JosVanEijndhoven/diyaudio-dac-preamp/dacxo-hw/PCBs/PCB-dacxo/kicad/daconv.sch

## KiCad design dacxo-hw/PCBs/PCB-dacxo/kicad/daconv.sch (2025-12-10)

Schematic: daconv.sch

Parts:
C301, C305, C336, C337: 100nF; C0805
C302, C304, C307, C314, C322, C323, C332, C334, C338: 1uF; C0805
C303, C306, C308, C311, C312, C313, C315, C318, C319, C325, C328, C331, C333: 10nF; C0805
C309, C310, C316, C317: 47uF; SM1206POL
C320, C321, C339: 1mF; CL-10
C324, C327: 1nF; C0805
C326, C329, C330, C335: 10uF; SM1206POL
D301, D302, D303: B130; DO214
FB301, FB302, FB303, FB304: FILTER; L0805
K301: PCM-audio_L; SIL-3-screw
K302: PCM-audio_R; SIL-3-screw
P301: CONN_4; SIL-4
P302: CONN_8; SIL-8
Q301, Q302: BCP54; SOT223-BCP
R303, R309: 10k; MMB0207
R306: 47R; R0805
R307: 3k3; R0805
R308, R316: 100R; R0805
R310, R314, R315: 1.5k; R0805
R312: 470R; R0805
R317, R318, R319: 470; R0805
R320: 100; R0805
U301, U305: PCM1792A; SSOP28
U302: ADR381; SOT23
U303: OPA2227; SO8E
U304: STM1816; SOT23
U306: MACHXO2-100; TQFP_100
U307: 74AC174; SO16E

Notes on the sheet:
I2S format: MSB first, wck low means left audio, 2x32 bitclk's in a wck period. wck and data change at falling edge of bitclk, are sampled at rising edge. MSB bit transfered at 2nd rising edge of bitclk after wck transient.
NP0
16V
2x7Vac
Analog supply
low noise
tantaal SMD elco AVX F930J476MAA
16V SMD 10mm dia
addr0: differentiate or unite both PCMs
