JosVanEijndhoven/diyaudio-dac-preamp/dacxo-hw/PCBs/PCB-dacxo/kicad/dacwolfs.sch

## KiCad design dacxo-hw/PCBs/PCB-dacxo/kicad/dacwolfs.sch (2025-12-10)

Schematic: dacwolfs.sch

Parts:
C201, C203, C205, C211, C213, C219: 100nF; C0805
C202, C204, C206, C207, C208, C212, C214, C215, C216: 10uF; SM1206POL
C209, C210, C217, C218: 10nF; C0805
FB201, FB202, FB203: FILTER; L0805
K201: WM-audio-L; SIL-3-screw
K202: WM-audio-R; SIL-3-screw
R202, R203, R204, R205, R206, R207, R208, R209: 470; R0805
R210, R211, R212, R213: 47r; R0805
R214, R215: 4.7k; R0805
U201, U202: WM8741; SSOP28

Notes on the sheet:
C1206C106K4RACAUTO
2x470 ohm to 10nF gives 67kHz bandwidth. Audio-grade: C0G dielektricum
WM8741 operated in software mode: status is written by microcontroller. It seems that this device does not support read-back of register data :-(
mount in HW mode
