JosVanEijndhoven/diyaudio-dac-preamp/dacxo-hw/PCBs/PCB-dacxo/kicad/pwr_clk.sch

## KiCad design dacxo-hw/PCBs/PCB-dacxo/kicad/pwr_clk.sch (2025-12-10)

Schematic: pwr_clk.sch

Parts:
C401, C404, C405, C408, C410, C415, C416, C417: 10nF; C0805
C402, C403, C406, C407, C409, C411, C412, C413, C424: 1uF; C0805
C414: 100nF; C0805
C423: 10uF; SM1206POL
C425, C426: 100pF; C0805
D401, D402: B130; DO214
D403, D404, D405, D406, D407: BI_LED; dualled-1210
FB401, FB402, FB403, FB404: FILTER; L0805
P401: 5V-in; SIL-3-screw
P402: I2C-in; SIL-4
P404: CONN_8; SIL-8
P405: test-jtag; SIL-8
P406: test-XO; SIL-8
P407: test-speed; SIL-8
P408: I2S; SIL-4
Q401: NUD3112; SC-74
R401, R402, R403, R404, R405, R418, R419, R420, R421, R422: 4k7; R0805
R406, R407, R408, R409, R410, R412, R414, R415, R416, R417: 330R; R0805
R411, R413: 47R; R0805
U306: MACHXO2-100; TQFP_100
U401: DLP-USB1232H
U403: TS3A5018; SO16E
U404, U407: XO; CCHD-957
U405: 1G99; SSOP8
U406: MC33275-3.3; SOT223-BCP

Notes on the sheet:
USB
in=0 then NC
I2C from controller
5V power in
test pins
45.1584MHz
49.152MHz
CCHD-957
48kHz
96kHz
192kHz: both
clk adjust
LCMXO2-1200HC-4TG100C
reserved for aux I2S input
input switch debounce
pin 8 and 15not on gnd in 201502 PCB!
