JosVanEijndhoven/diyaudio-dac-preamp/dacxo-hw/PCBs/PCB-dacxo/kicad/recvr.sch

## KiCad design dacxo-hw/PCBs/PCB-dacxo/kicad/recvr.sch (2025-12-10)

Schematic: recvr.sch

Parts:
C501, C504, C505, C507, C509: 10nF; C0805
C502, C503, C506, C508, C510: 1uF; C0805
C511, C512, C513, C515, C517: 100nF; C0805
C514: 1nF; C0805
C516: 22nF; C0805
FB501, FB502, FB503: FILTER; L0805
P501: aux-in; SIL-4
P502: DUAL-CINCH; dualphono-kobiconn
R501, R502, R503, R504, R505, R506, R507, R508, R511: 47k; R0805
R509, R510: 47R; R0805
R513, R514, R523, R524: 150; R0805
R520, R529: 1k; R0805
R522: 3k3; R0805
T501, T502: PE-65812NL; SPDIFtrafo-pulse
U306: MACHXO2-100; TQFP_100
U501, U502: TORX; TORX-PLR135
U503: CS8416; SO28

Notes on the sheet:
P4[28] and P4[29] are still avail for UART3 TXD and RXD, are connected to daughterboard pins PAD15 and PAD16. (Maybe some UART should be routed to mainboard IO in next rev.)
PLR135T7
SW mode
HW mode
2xR for SW mode
pull-down resistor on RST was missing
