JosVanEijndhoven/diyaudio-dac-preamp/dacxo-hw/PCBs/PCB-opampout/kicad/audio-left.sch

## KiCad design dacxo-hw/PCBs/PCB-opampout/kicad/audio-left.sch (2025-12-10)

Schematic: audio-left.sch

Parts:
C301, C302: 470pF; Cmica6
K203, K204, K205, K206: CINCH-DUAL; switchcraft-dualcinch
K209, K210, K211, K212, K213, K316: RELAY_G6K_AB; G6K-2F-Y
K301, K302: XLR3-FEMALE; NC3FAH
K307, K308, K309, K310, K311, K312, K313, K314: RELAY_G6K; G6K-2F-Y
K315: XLR3-MALE; NC3MAH
R301, R303, R320, R335: 1k; MMB0207
R302, R334: inf; MMB0207
R304, R314, R321, R331: 470R; MMB0207
R305, R322: 3k9; MMB0207
R306, R323: 0R; MMB0207
R307, R324: 100R; MMB0207
R308, R325: 2k2; MMB0207
R309, R326: 220R; MMB0207
R310, R327: 1k2; MMB0207
R311, R328: 560R; MMB0207
R312, R329: 680R; MMB0207
R313, R318, R330, R336: 1k8; MMB0207
R315, R332: 12K; MMB0207
R316, R333: 390R; MMB0207
R317, R319: 47k; MMB0207
U301: LME49720; DIP-8__300
