JosVanEijndhoven/diyaudio-dac-preamp/dacxo-hw/PCBs/PCB-opampout/kicad/audio-right.sch

## KiCad design dacxo-hw/PCBs/PCB-opampout/kicad/audio-right.sch (2025-12-10)

Schematic: audio-right.sch

Parts:
C201, C203, C205, C207: 10n; Cmica6-w0805
C202, C204, C206, C208: 10n; SM0805
K201: CINCH-DUAL; dualphono-kobiconn
K202: Vin-L; SIL-3
K203, K207: RELAY_G6K; G6K-2F-Y
K204: Vout-L; NC3MAH
K205: Iin-L; SIL-3
K206: Vin-R; SIL-3
K208: Vout-R; NC3MAH
K209: Iin-R; SIL-3
L201, L202, L203, L204: 330uH; SM1210
R201, R206, R210, R211, R212, R216, R221, R222, R223, R228, R232, R233, R234, R238, R243, R244: inf; SMM0204
R202, R203, R204, R208, R209, R213, R214, R218, R219, R220, R224, R225, R226, R230, R231, R235, R236, R240, R241, R242: 2k; SMM0204
R205, R215, R227, R237: 220R; SMM0204
R207, R217, R229, R239: 249; SMM0204
U201, U202, U203, U204: LME49720; DIP-8__300

Notes on the sheet:
TDK NLV32T 331J
G6K-2Y-5
-20dB switch
all 12 of 2k resistors around opamps are 0.1% MELF 0204
Voltage input 2x 2.5Vdc +/- 1.4Vpk
Current input: 2x 12.4mAdc +/- 7.8mApk
all 12 resistors around opamps are 0.1% MELF 0204
