JosVanEijndhoven/diyaudio-dac-preamp/dacxo-hw/PCBs/PCB-opampout/kicad/control.sch

## KiCad design dacxo-hw/PCBs/PCB-opampout/kicad/control.sch (2025-12-10)

Schematic: control.sch

Parts:
C501, C502, C503, C504, C505, C506, C507, C508, C509, C510, C511, C512: 1uF; SM0805
C513: 100nF; SM0805
C514: 100nF; CAPX2
D501: BAS116; SOT23-diode
JP501, JP502, JP503: JUMPER3A; SIL-3
K501: RELAY_G5SB; Relay-G5SB
P501: I2C; termblock-4x2.54
P502: TERMBLOCKX4; termblockx4
P503: Chassis; termblock-4x2.54
R501, R502, R503, R504, R505, R506, R507, R508, R509, R510, R511, R512, R513, R514: 4k7; R0805
U501: 74HC00; SO14E
U502: 74HC238; SO16E
U503, U504, U506: ULN2003; SO16E
U505: MCP23017; SO28
VR501: 400V; Varistor-5mm

Notes on the sheet:
0 D 5 C
P503 provides a connection for an optional external power-switch relay, an audio mute relay, and for a wire to chassis ground.
+ P M C
IN OUT
Varistor to damp spikes from switching the transformer
capacitor 250VAC class X2 safety
The PIC controls the relay state by sending a 16-bit word through I2C into the MCP23017. In stand-by mode (and after reset): - the 16-bit code is all-0 - none of the relays is powered - the attenuator chain is at max attenuation - none of the input channels is selected.
Switch for analog power supply transformer and/or other audio equipment (230VAC)
Through P501, the I2C connected display board receives power. If the display board is powered externally (eg through USB), D501 prevents power to flow into the relay board.
Keep receiver in reset if I2C has power, but relay board has not.
